peterheinrich/InternetOverSpaghetti/doc/IPoS_PCB_3D.png

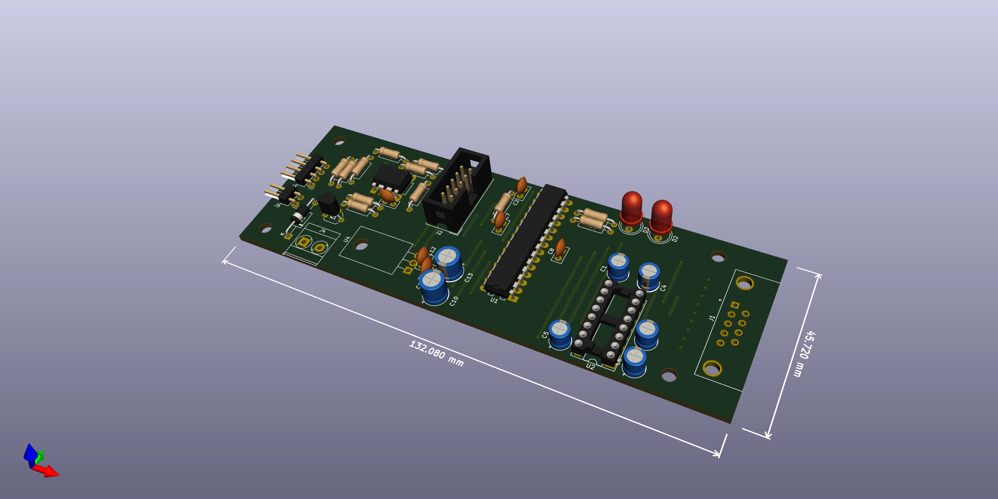
doc/IPoS_PCB_3D.png
