peterheinrich/InternetOverSpaghetti/doc/06_FinishedBidriectionalAssembly.JPG

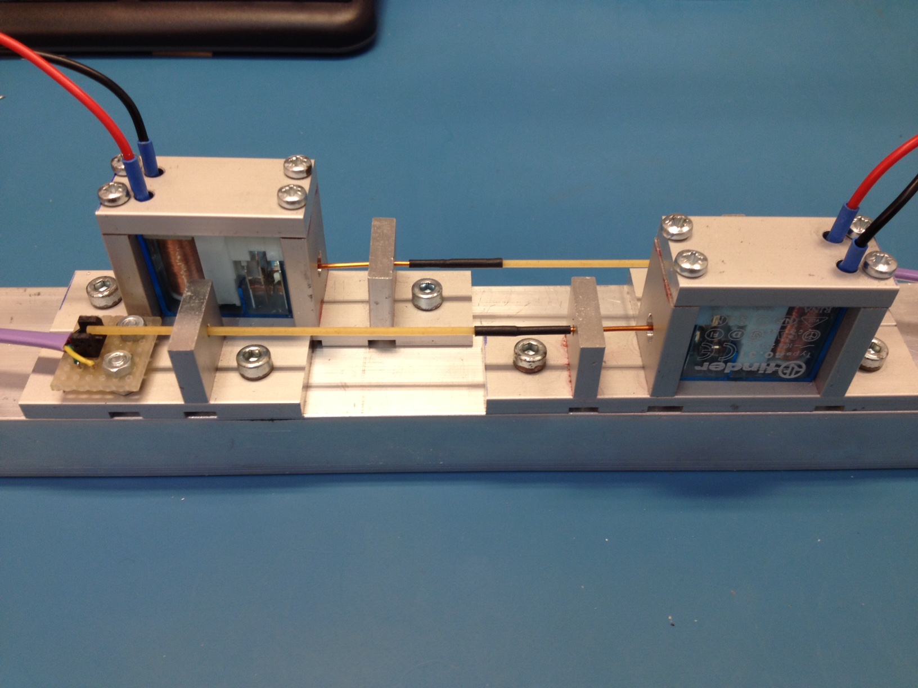
doc/06_FinishedBidriectionalAssembly.JPG
