peterheinrich/InternetOverSpaghetti/doc/09_CompleteAssemblyDetail.JPG

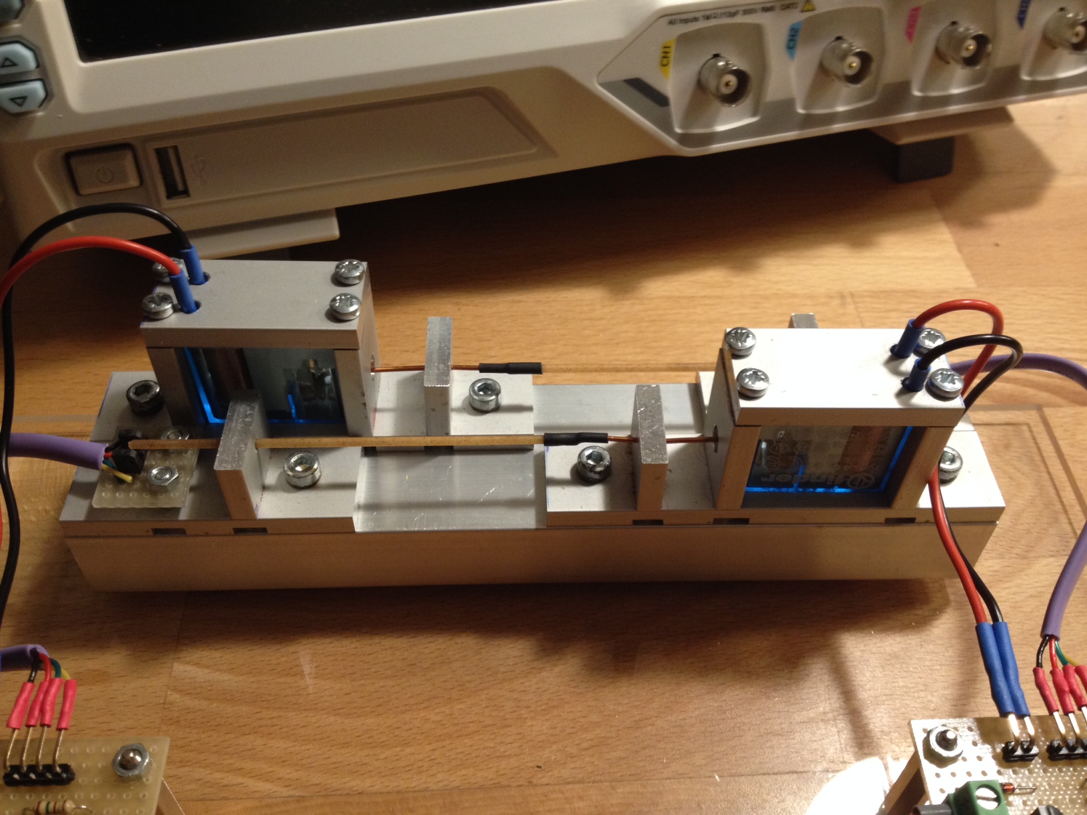
doc/09_CompleteAssemblyDetail.JPG
